tmsaavedra/ESPHOME_Doorbell/IMG_2008.JPG

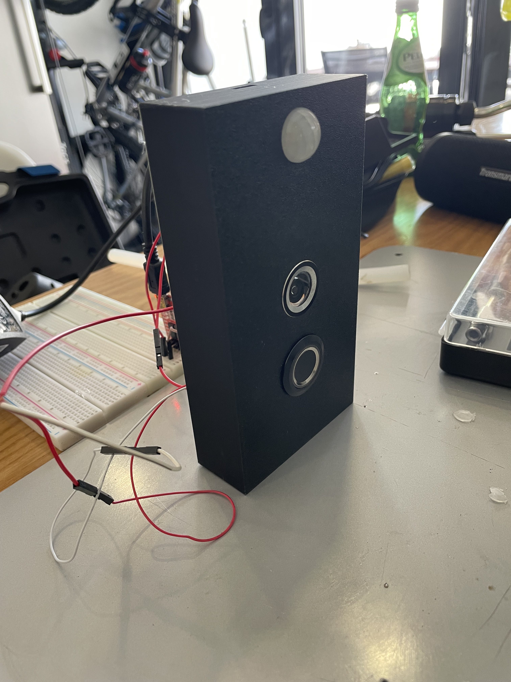
IMG_2008.JPG
